birkler/ipod_2_bluetooth_a2dp/electrical/ipod_a2dp_kicad/ipoad_a2dp/ipoad_a2dp.kicad_pcb

## KiCad design modules/05-simonSays/SS01-circuit/simon_says.kicad_sch

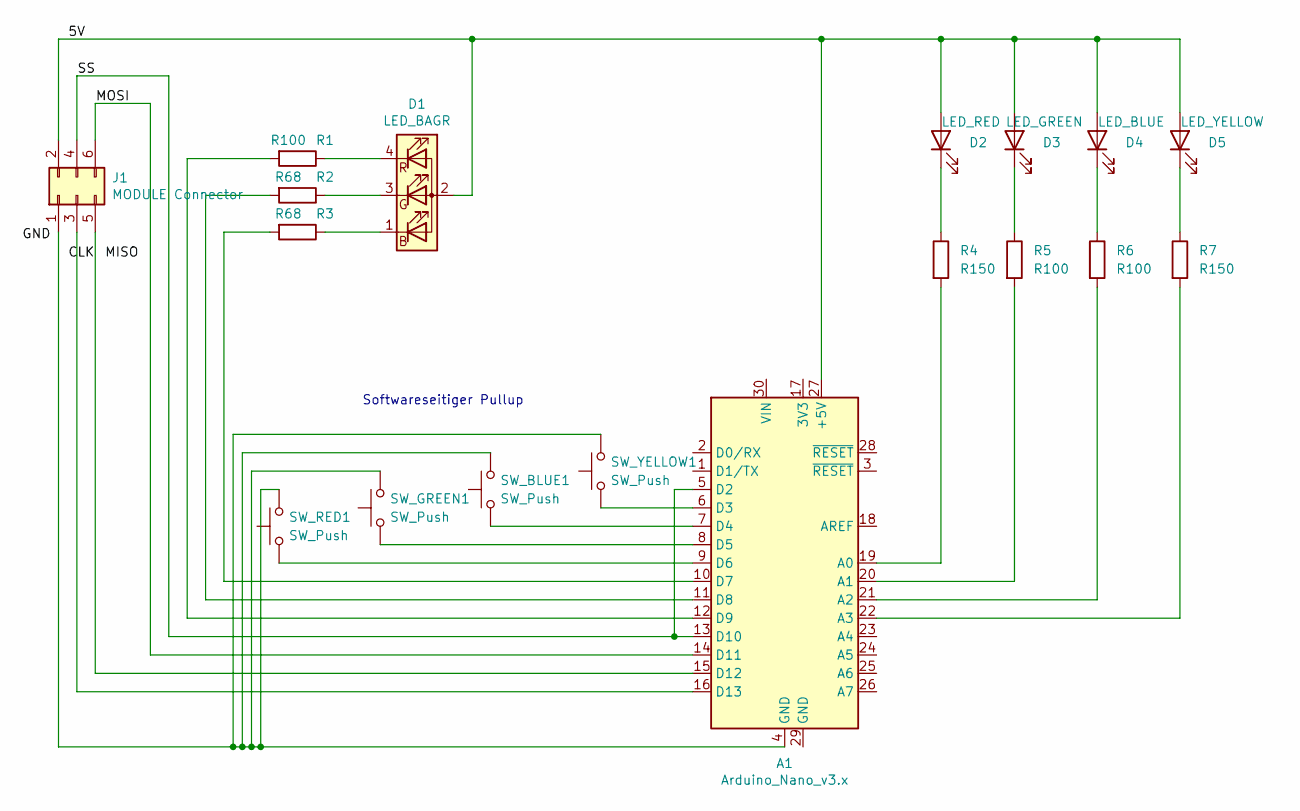
[picture p2: schematic simon_says.kicad_sch]

Parts:
A1: Arduino_Nano_v3.x; Arduino_Nano
D1: LED_BAGR
D2: LED_RED
D3: LED_GREEN
D4: LED_BLUE
D5: LED_YELLOW
J1: MODULE Connector
R1, R5, R6: R100
R2, R3: R68
R4, R7: R150
SW_BLUE1: SW_Push
SW_GREEN1: SW_Push
SW_RED1: SW_Push
SW_YELLOW1: SW_Push

Connections:
5V: A1.27 (+5V), D1.2 (A), D2.2 (A), D3.2 (A), D4.2 (A), D5.2 (A), J1.2
MOSI: A1.14 (D11), J1.6
unnamed: A1.4 (GND), J1.1, SW_BLUE1.2, SW_GREEN1.2, SW_RED1.2, SW_YELLOW1.2
unnamed: A1.6 (D3), SW_YELLOW1.1
unnamed: A1.7 (D4), SW_BLUE1.1
unnamed: A1.8 (D5), SW_GREEN1.1
unnamed: A1.9 (D6), SW_RED1.1
unnamed: A1.10 (D7), R3.2
unnamed: A1.11 (D8), R2.2
unnamed: A1.12 (D9), R1.2
unnamed: A1.15 (D12), J1.5
unnamed: A1.16 (D13), J1.3
unnamed: A1.19 (A0), R4.2
unnamed: A1.20 (A1), R5.2
unnamed: A1.21 (A2), R6.2
unnamed: A1.22 (A3), R7.2
unnamed: D1.1 (BK), R3.1
unnamed: D1.3 (GK), R2.1
unnamed: D1.4 (RK), R1.1
unnamed: D2.1 (K), R4.1
unnamed: D3.1 (K), R5.1
unnamed: D4.1 (K), R6.1
unnamed: D5.1 (K), R7.1
SS: A1.5 (D2), A1.13 (D10), J1.4

Notes on the sheet:
Softwareseitiger Pullup
